Jacobgarm/P3Wireless/EagleSketches/Server/Server/Server wire chart.sch

## EAGLE design EagleSketches/Server/Server/Server wire chart.sch (2022-02-04)

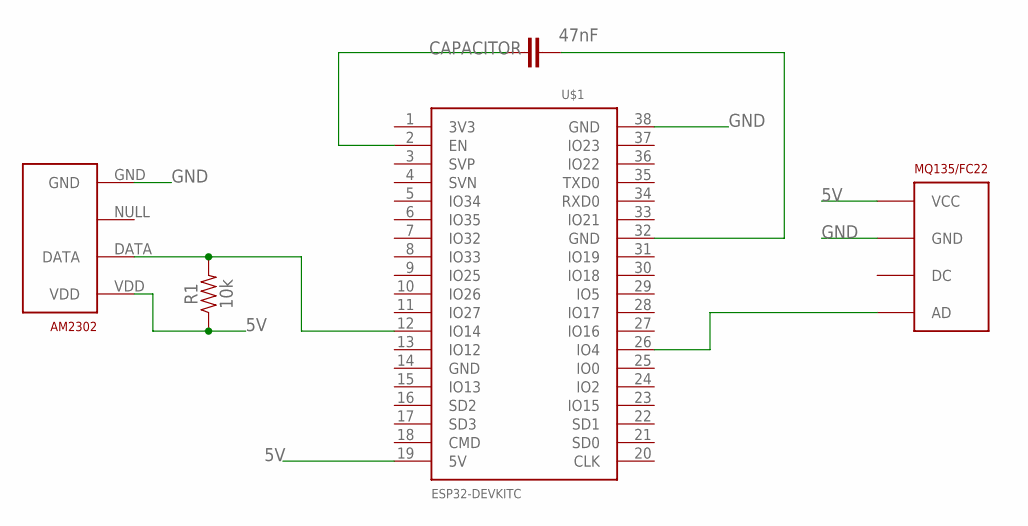
[picture p3: schematic Server wire chart.sch]

Parts:
AM2302: RHT03_DHT-22_AM2302; RHT03_DHT-22
CAPACITOR: 47nF; C2.5-3
MQ135/FC22: MQ; RHT03_DHT-22
R1: 10k; 0402
U$1: ESP32DEVKITC; ESP32-DEVKITC

Connections:
5V: AM2302.VDD, MQ135/FC22.VDD (VCC), R1.1, U$1.19 (5V)
GND: AM2302.GND, MQ135/FC22.DATA (GND), U$1.38 (GND)
unnamed: MQ135/FC22.GND (AD), U$1.26 (IO4)
unnamed: AM2302.DATA, R1.2, U$1.12 (IO14)
unnamed: CAPACITOR.1, U$1.2 (EN)
unnamed: CAPACITOR.2, U$1.32 (GND)
